nfranzwa/OscillatingPump/ESP32_CTRL/include/wavegen.h

#ifndef WAVE_GENERATOR_H
#define WAVE_GENERATOR_H
#include <Arduino.h>
#include <string>
class WaveGenerator {
private:
    // waveform parameters (ms)
    int* ASDR; // rise, sustain, decay, rest
    // int* ASDR_new; // redundant?
    int cyclePeriod;
    int cycleFreq;
    unsigned long lastCycleStart=0;
    int PWM_min;
    int PWM_max;
    String transition;
    int PWM_value;
public:
    WaveGenerator(int pwm_min, int pwm_max, String trn="linear") :
        PWM_min(pwm_min),PWM_max(pwm_max), transition(trn)
        {
            ASDR = new int[4]{250,250,250,250};
        }
    float getFrequency(){return 1000.0/cyclePeriod;} //frequency in Hz
    int getPeriod(){return ASDR[0]+ASDR[1]+ASDR[2]+ASDR[3];} //period in ms
    String getTransition() {return transition;}
    void updateParams(int* new_asdr,int pwm_min, int pwm_max);//update the ASDR and PWM range
    int generatePWM();
    void update(int* ADSR,int min_PWM,int max_PWM,bool debug=false);
};
int mapPos(float P_target);
#endif
